hipe-0/StaffTrainer/medias/20240603_070924.jpg

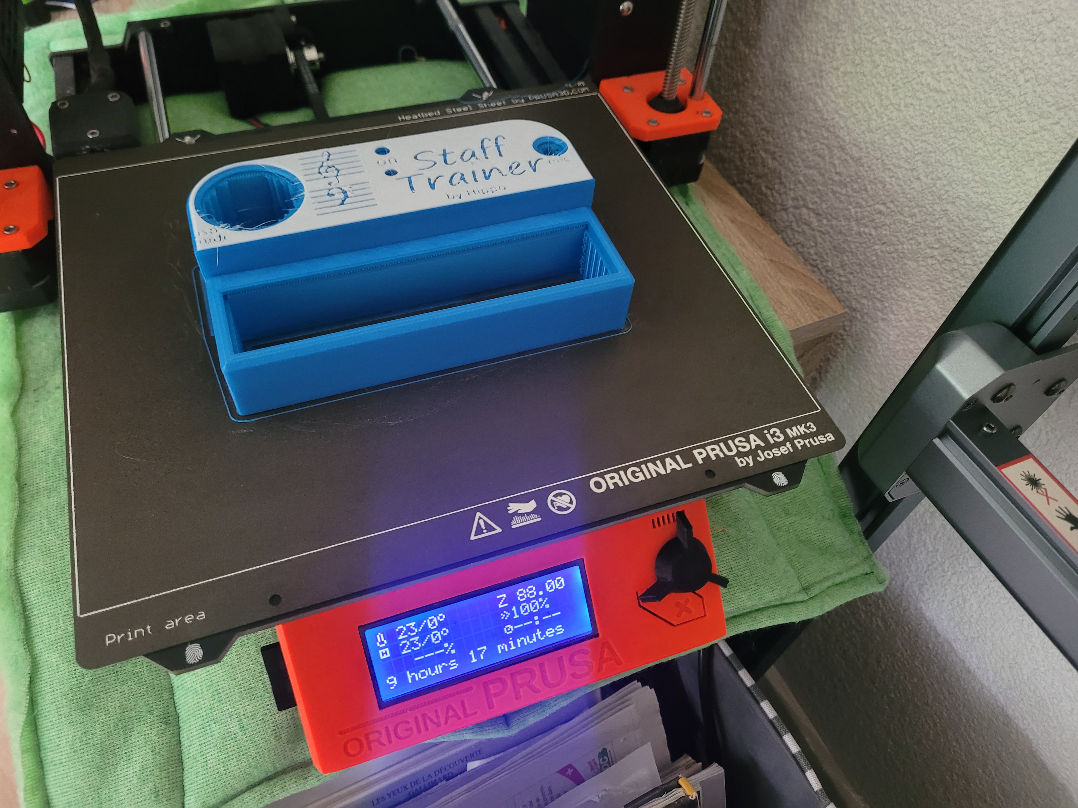
medias/20240603_070924.jpg
