hipe-0/StaffTrainer/source/StaffTrainer_v0_14_white_background/Bitmaps.h

// go to https://javl.github.io/image2cpp/

// 'BassClef', 52x57px
const unsigned char BitmapBassClef [] PROGMEM = {
	0x00, 0x01, 0xff, 0xc0, 0x00, 0x00, 0x00, 0x00, 0x0f, 0xff, 0xf8, 0x00, 0x00, 0x00, 0x00, 0x3f, 
	0xff, 0xfe, 0x00, 0x00, 0x00, 0x00, 0x7c, 0x01, 0xff, 0x00, 0x00, 0x00, 0x00, 0xe0, 0x00, 0x7f, 
	0xc0, 0x00, 0x00, 0x01, 0xc0, 0x00, 0x3f, 0xe0, 0x07, 0xc0, 0x03, 0x80, 0x00, 0x1f, 0xe0, 0x0f, 
	0xe0, 0x07, 0x00, 0x00, 0x0f, 0xf0, 0x0f, 0xf0, 0x0e, 0x00, 0x00, 0x07, 0xf8, 0x0f, 0xf0, 0x0e, 
	0x00, 0x00, 0x07, 0xf8, 0x0f, 0xf0, 0x1c, 0x00, 0x00, 0x03, 0xfc, 0x0f, 0xf0, 0x18, 0x00, 0x00, 
	0x03, 0xfc, 0x07, 0xe0, 0x38, 0xf8, 0x00, 0x01, 0xfe, 0x03, 0xc0, 0x3b, 0xfe, 0x00, 0x01, 0xfe, 
	0x00, 0x00, 0x3f, 0xff, 0x00, 0x01, 0xfe, 0x00, 0x00, 0x3f, 0xff, 0x80, 0x01, 0xfe, 0x00, 0x00, 
	0x3f, 0xff, 0x80, 0x01, 0xff, 0x00, 0x00, 0x3f, 0xff, 0x80, 0x00, 0xff, 0x00, 0x00, 0x3f, 0xff, 
	0xc0, 0x00, 0xff, 0x00, 0x00, 0x3f, 0xff, 0xc0, 0x00, 0xff, 0x00, 0x00, 0x3f, 0xff, 0xc0, 0x00, 
	0xff, 0x00, 0x00, 0x3f, 0xff, 0x80, 0x00, 0xff, 0x00, 0x00, 0x1f, 0xff, 0x80, 0x00, 0xff, 0x03, 
	0xc0, 0x0f, 0xff, 0x00, 0x00, 0xff, 0x07, 0xe0, 0x0f, 0xfe, 0x00, 0x00, 0xff, 0x0f, 0xf0, 0x03, 
	0xfc, 0x00, 0x01, 0xff, 0x0f, 0xf0, 0x00, 0x00, 0x00, 0x01, 0xff, 0x0f, 0xf0, 0x00, 0x00, 0x00, 
	0x01, 0xfe, 0x0f, 0xf0, 0x00, 0x00, 0x00, 0x01, 0xfe, 0x0f, 0xe0, 0x00, 0x00, 0x00, 0x03, 0xfe, 
	0x07, 0xc0, 0x00, 0x00, 0x00, 0x03, 0xfe, 0x00, 0x00, 0x00, 0x00, 0x00, 0x03, 0xfc, 0x00, 0x00, 
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
	0x1f, 0xff, 0xff, 0x80, 0x0f, 0xff, 0xff, 0x00, 0x07, 0xff, 0xfe, 0x00, 0x07, 0xff, 0xfe, 0x00, 
	0x07, 0xff, 0xfe, 0x00, 0x07, 0xff, 0xfe, 0x00, 0x0f, 0xff, 0xff, 0x00, 0x0f, 0xff, 0xff, 0x00, 
	0x0f, 0xff, 0xff, 0x00, 0x0f, 0xf9, 0xff, 0x00, 0x0f, 0xe0, 0x7f, 0x00, 0x07, 0x80, 0x1e, 0x00
};
