hipe-0/StaffTrainer/medias/20240531_105259.jpg

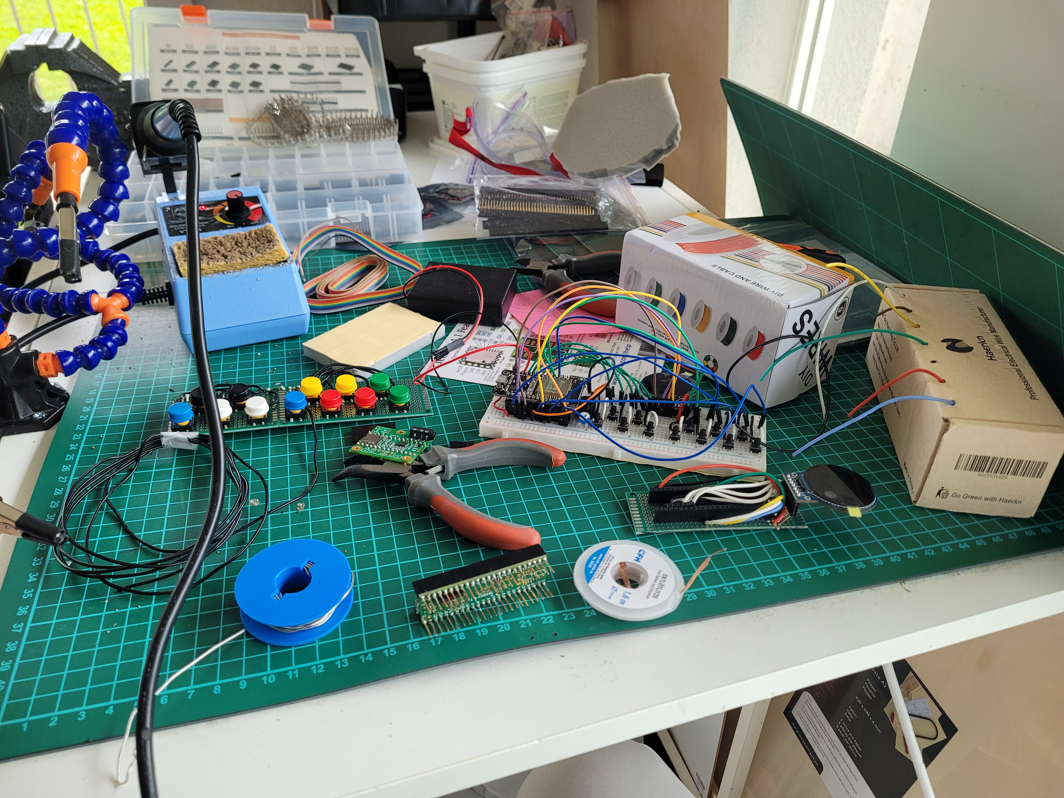
medias/20240531_105259.jpg
