hipe-0/StaffTrainer/medias/20240602_180305.jpg

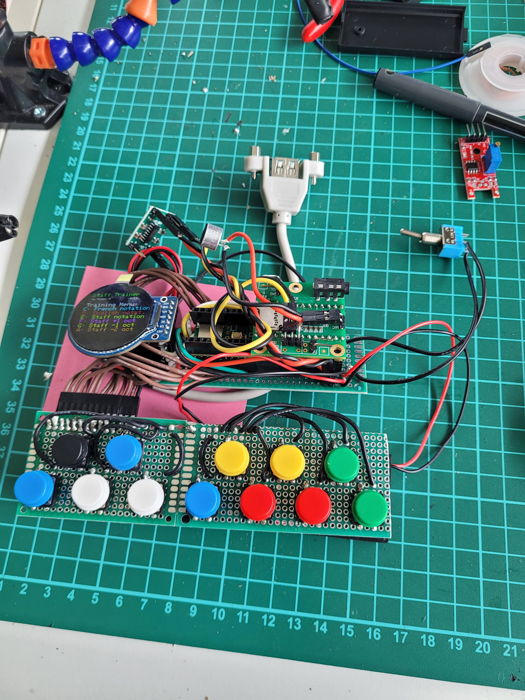
medias/20240602_180305.jpg
