hipe-0/StaffTrainer/medias/20240602_200627.jpg

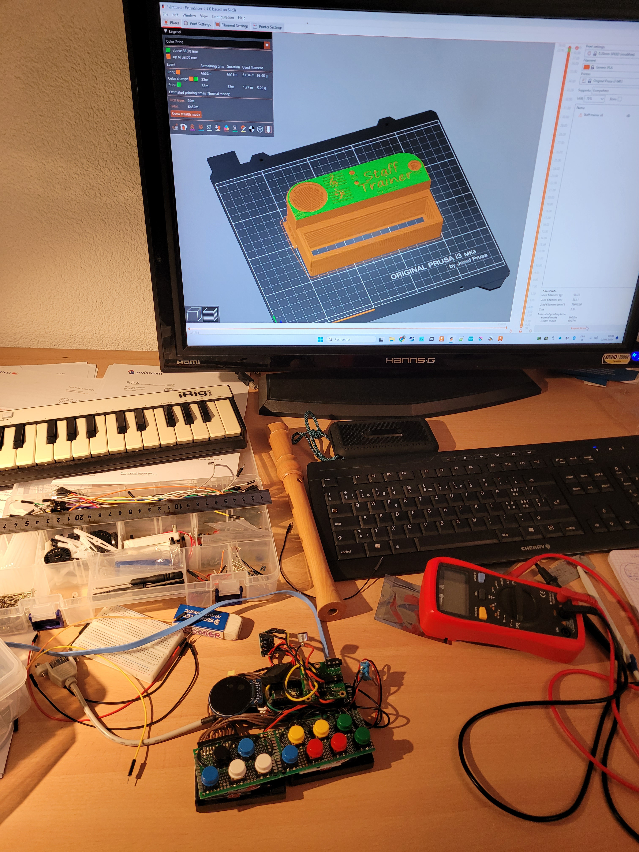
medias/20240602_200627.jpg
