hipe-0/StaffTrainer/medias/20240602_210528.jpg

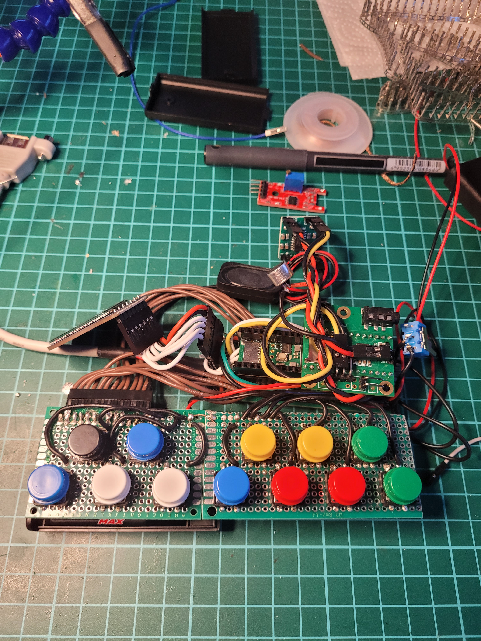
medias/20240602_210528.jpg
