hipe-0/StaffTrainer/medias/20240602_210846.jpg

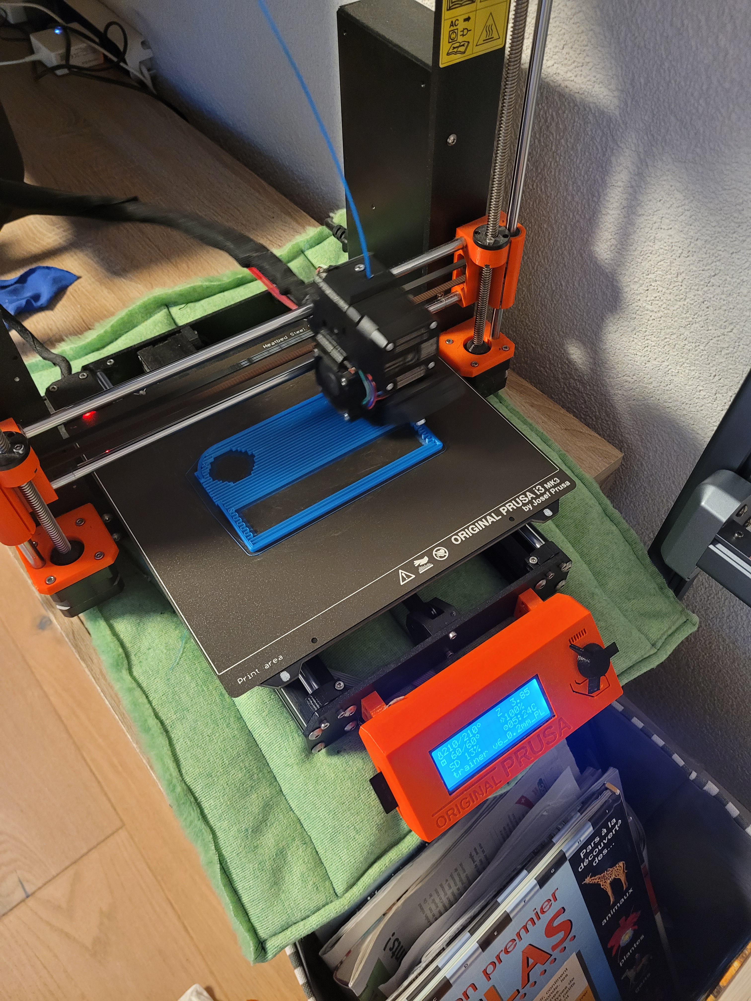
medias/20240602_210846.jpg
