hipe-0/StaffTrainer/medias/20240602_215317.jpg

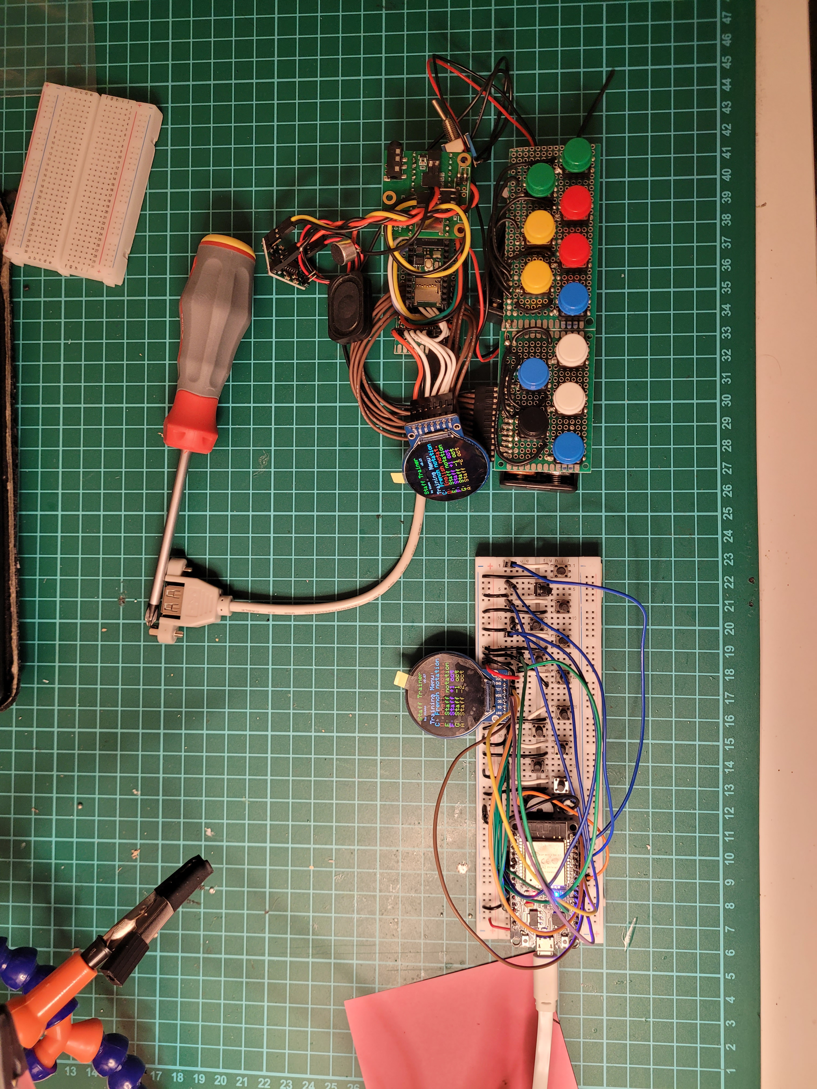
medias/20240602_215317.jpg
