hipe-0/StaffTrainer/medias/20240603_094652.jpg

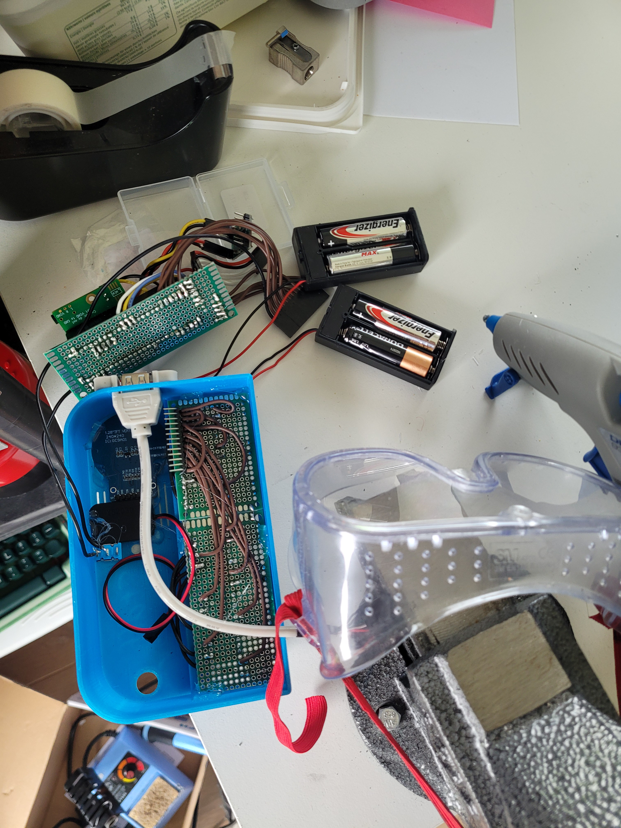
medias/20240603_094652.jpg
