hipe-0/StaffTrainer/medias/20240603_203550.jpg

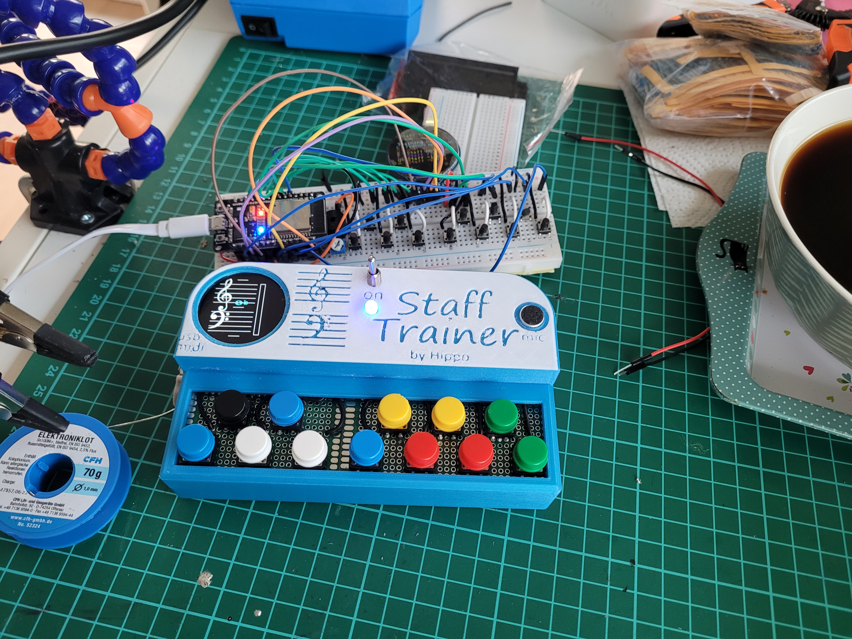
medias/20240603_203550.jpg
