hipe-0/StaffTrainer/medias/20240603_233740.jpg

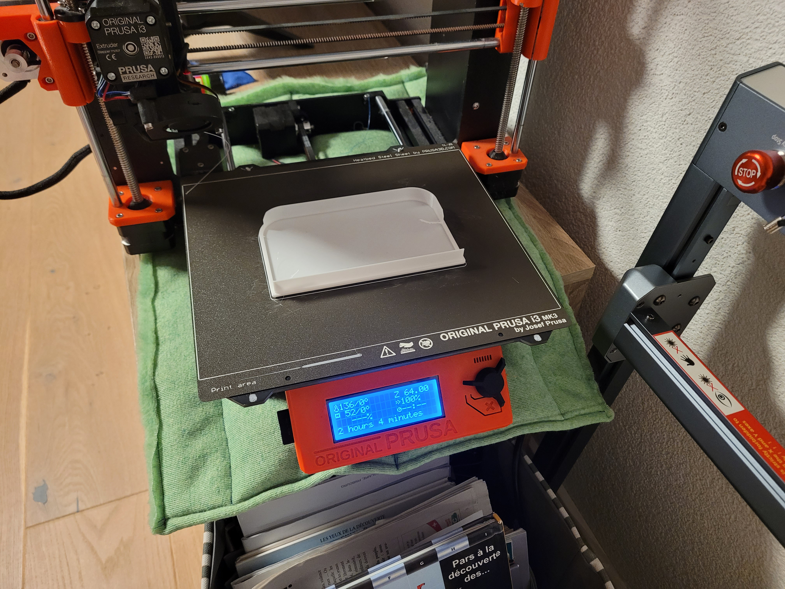
medias/20240603_233740.jpg
