hipe-0/StaffTrainer/medias/20240603_234205.jpg

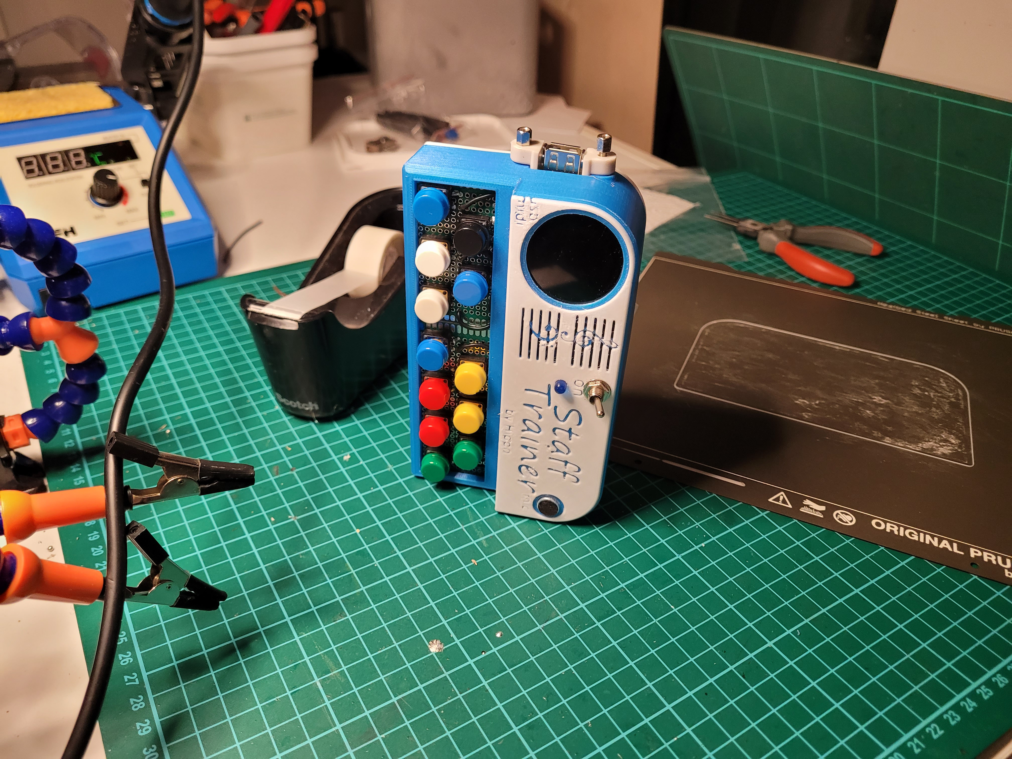
medias/20240603_234205.jpg
