hipe-0/StaffTrainer/medias/20240617_161215.jpg

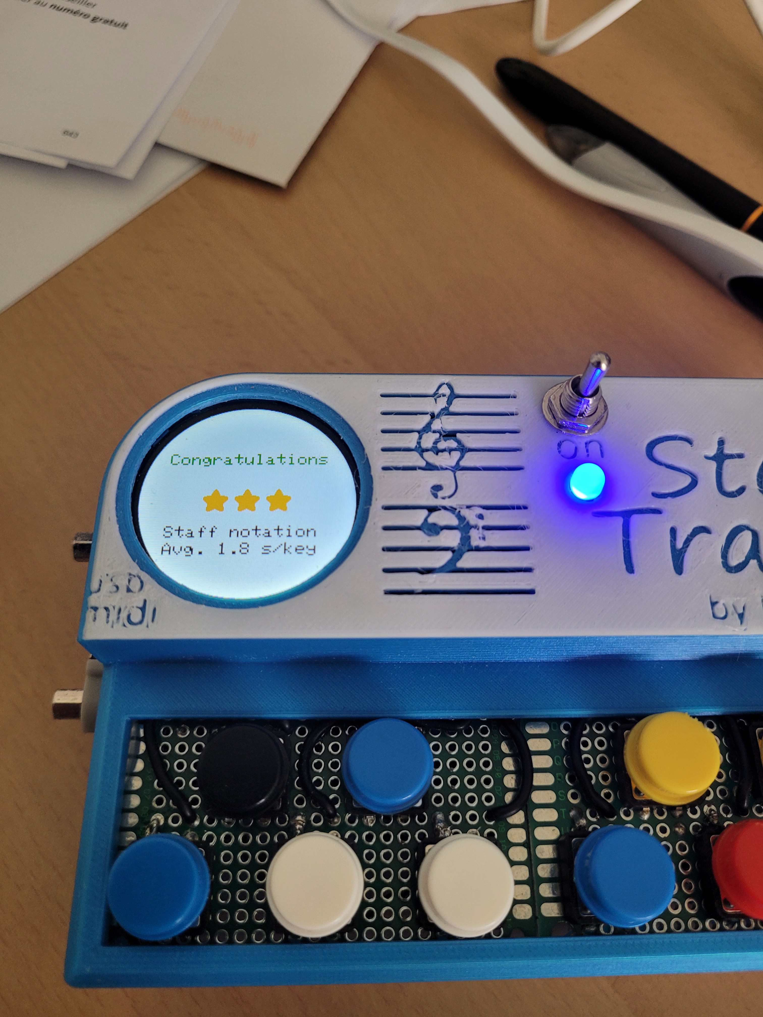
medias/20240617_161215.jpg
