hipe-0/StaffTrainer/medias/20240623_124636.jpg

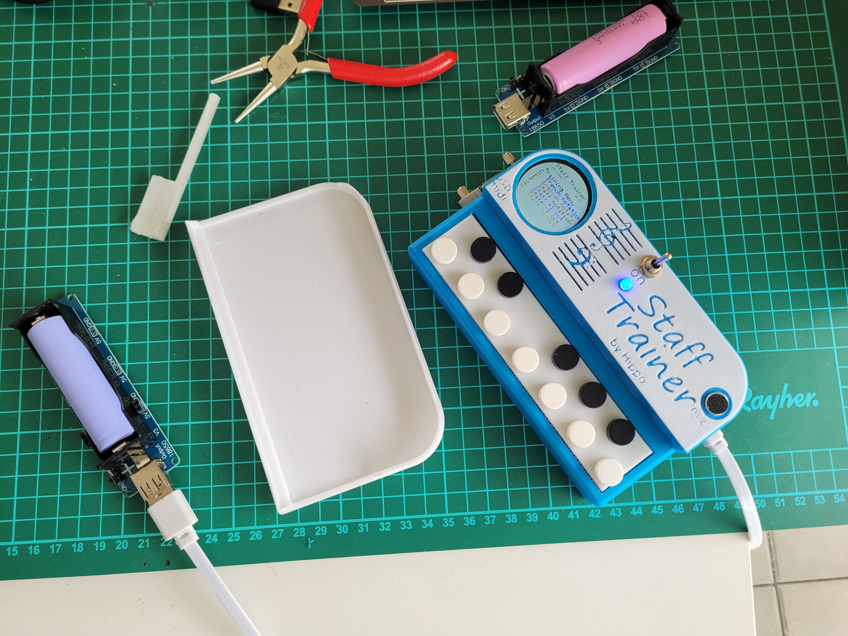
medias/20240623_124636.jpg
